notjerrygoh/Team-JRC-WRO-Future-Engineers-Engineering-Journal/schemes/Team JRC Robot Schematic Diagram (LT Spice Software)/Draft2.asc

BATTERY: voltage; 9V
X1: Rpi4B
X2: Ultrasonic
X3: Ultrasonic
X4: Ultrasonic
X5: Ultrasonic
X6: MotorDriver
X7: Motor
X8: Motor
X9: Servo
Named nets: 0, 5V_SHARED
