notjerrygoh/Team-JRC-WRO-Future-Engineers-Engineering-Journal/src/newdetect.py

# Run sudo pigpiod in terminal before running code

from gpiozero import Button, DistanceSensor
from gpiozero.pins.pigpio import PiGPIOFactory
from time import time
import pigpio
import numpy as np
import cv2
from picamera2 import Picamera2

pi = pigpio.pi()
button = Button(13, bounce_time=0.04, pull_up=True)

# Ultrasonic sensors
factory = PiGPIOFactory()
frontultrasonic = DistanceSensor(echo=5, trigger=6, max_distance=4, pin_factory=factory)
leftultrasonic = DistanceSensor(echo=17, trigger=4, max_distance=4, pin_factory=factory)
rightultrasonic = DistanceSensor(echo=27, trigger=22, max_distance=4, pin_factory=factory)
backultrasonic = DistanceSensor(echo=19, trigger=26, max_distance=4, pin_factory=factory)

turn_amt = 300
base_speed = 76
offset = 0

# Servo
servo_pin = 16
pwm = pigpio.pi()
pwm.set_mode(servo_pin, pigpio.OUTPUT)
pwm.set_PWM_frequency(servo_pin, 50)
pwm.set_servo_pulsewidth(servo_pin, 1500 + offset)  

# Camera
cam = Picamera2()
cam.configure(cam.create_preview_configuration({"size": (640, 360)}))
cam.start()


# Motors
M1A = 23
M1B = 24
pi.set_mode(M1A, pigpio.OUTPUT)
pi.set_mode(M1B, pigpio.OUTPUT)

# Motor speed
def motorSpeed(speed):
    if speed < 0:
        pi.set_PWM_dutycycle(M1A, abs(speed))
        pi.set_PWM_dutycycle(M1B, 0)
    elif speed > 0:
        pi.set_PWM_dutycycle(M1A, 0)
        pi.set_PWM_dutycycle(M1B, abs(speed))
    else:
        pi.set_PWM_dutycycle(M1A, 0)
        pi.set_PWM_dutycycle(M1B, 0)

# Orange line detection
last_orange_seen = -1
def detect_orange(frame, on_orange_line, lap_count):
    global last_orange_seen
    hsvFrame = cv2.cvtColor(frame, cv2.COLOR_BGR2HSV)
    orange_lower = np.array([5, 150, 150], np.uint8)
    orange_upper = np.array([20, 255, 255], np.uint8)
    orange_mask = cv2.inRange(hsvFrame, orange_lower, orange_upper)

    height, width = orange_mask.shape
    roi = orange_mask[height-60:height, :]
    orange_pixels = cv2.countNonZero(roi)

    ctime = time()
    crossed = False
    if orange_pixels > 1100:
        if not on_orange_line and (ctime - last_orange_seen) > 1.6:
            lap_count += 1
            crossed = True
            on_orange_line = True
            last_orange_seen = ctime
        elif (ctime - last_orange_seen) <= 1.6:
            print("Orange double count prevented")
    else:
        on_orange_line = False

    return lap_count, on_orange_line, crossed

# --- Blue line detection ---
last_blue_seen = -1
def detect_blue(frame, on_blue_line, lap_count):
    global last_blue_seen
    hsvFrame = cv2.cvtColor(frame, cv2.COLOR_BGR2HSV)
    blue_lower = np.array([100, 150, 20], np.uint8)
    blue_upper = np.array([130, 255, 255], np.uint8)
    blue_mask = cv2.inRange(hsvFrame, blue_lower, blue_upper)

    height, width = blue_mask.shape
    roi = blue_mask[height-60:height, :]
    blue_pixels = cv2.countNonZero(roi)

    ctime = time()

    crossed = False
    if blue_pixels > 1100:
        if not on_blue_line and (ctime - last_blue_seen) > 1.6:
            lap_count += 1
            crossed = True
            on_blue_line = True
            last_blue_seen = ctime
        elif (ctime - last_blue_seen) <= 1.6:
            print("Blue double count prevented")
    else:
        on_blue_line = False

    return lap_count, on_blue_line, crossed

# Red and green detection
def traffic_lights(frame):
    hsvFrame = cv2.cvtColor(frame, cv2.COLOR_BGR2HSV)

    # Red
    red_lower1 = np.array([0, 150, 50], np.uint8)
    red_upper1 = np.array([5, 255, 255], np.uint8)
    red_lower2 = np.array([172, 150, 100], np.uint8)
    red_upper2 = np.array([180, 255, 255], np.uint8)
    red_mask = cv2.inRange(hsvFrame, red_lower1, red_upper1) | cv2.inRange(hsvFrame, red_lower2, red_upper2)

    # Green
    green_lower = np.array([35, 50, 50], np.uint8)
    green_upper = np.array([85, 255, 255], np.uint8)
    green_mask = cv2.inRange(hsvFrame, green_lower, green_upper)

    kernel = np.ones((5, 5), "uint8")
    red_mask = cv2.dilate(red_mask, kernel)
    green_mask = cv2.dilate(green_mask, kernel)


    def detect_and_label(mask, color_bgr, label):
        contours, _ = cv2.findContours(mask, cv2.RETR_TREE, cv2.CHAIN_APPROX_SIMPLE)
        if not contours:
            return 0, None
        largest = max(contours, key=cv2.contourArea)
        area = cv2.contourArea(largest)
        if 20000 < area < 60000:  # stable area range
            x, y, w, h = cv2.boundingRect(largest)
            cv2.rectangle(frame, (x, y), (x + w, y + h), color_bgr, 2)
            return area, label
        return 0, None

    red_area, red_label = detect_and_label(red_mask, (0, 0, 255), "Red")
    green_area, green_label = detect_and_label(green_mask, (0, 255, 0), "Green")

    return red_area, green_area, red_label, green_label


lap_count = 0
on_orange_line = False
orange_sequence = None  
servo_sequence = None  
stable_counter = 0  
is_orange = 0

# wait for start
print("Waiting...")
button.wait_for_press()
print("Robot Started!")

try:
    while True:

        try:
            frame = cv2.cvtColor(cam.capture_array()[::-1, :, :3], cv2.COLOR_RGB2BGR)
            camera_ok = True
        except Exception:
            camera_ok = False

        distance_cm = frontultrasonic.distance * 100
        current_time = time()


        if camera_ok and lap_count < 12: 
            crossed = False
            if is_orange == 0:
                lap_count, on_orange_line, crossed = detect_orange(frame, on_orange_line, lap_count)
                if lap_count == 1:
                    is_orange = 1
                    turn_amt = 200
                else:
                    lap_count, on_orange_line, crossed = detect_blue(frame, on_orange_line, lap_count)
                    if lap_count == 1:
                        is_orange = -1
                        turn_amt = -200
            elif is_orange == 1:
                lap_count, on_orange_line, crossed = detect_blue(frame, on_orange_line, lap_count)
            elif is_orange == -1:
                lap_count, on_orange_line, crossed = detect_orange(frame, on_orange_line, lap_count)

            motorSpeed(base_speed)

            if crossed and orange_sequence is None:
                orange_sequence = ([(1500 + offset, 0), (1500 + offset + turn_amt, 1.7), (1500 + offset,0)], 0, current_time)
                print(f"Lap {lap_count} completed")

            if orange_sequence is not None:
                steps, step_index, start_time = orange_sequence
                pos, duration = steps[step_index]
                pwm.set_servo_pulsewidth(servo_pin, pos)

                if current_time - start_time >= duration:
                    step_index += 1
                    if step_index >= len(steps):
                        orange_sequence = None
                    else:
                        orange_sequence = (steps, step_index, current_time)

            red_area, green_area, red_label, green_label = traffic_lights(frame)

            if red_area > green_area or green_area > red_area:
                stable_counter += 1
            else:
                stable_counter = 0

            if servo_sequence is None and stable_counter >= 3: 
                if red_area > green_area:
                    servo_sequence = ([(1500 + offset + turn_amt, 1), (1500 + offset, 1), (1500 + offset - turn_amt, 1), (1500 + offset, 0)], 0, current_time + 0.1)
                    color_detected = red_label
                elif green_area > red_area:
                    servo_sequence = ([(1500 + offset - turn_amt, 1), (1500 + offset, 1), (1500 + offset + turn_amt, 1), (1500 + offset, 0)], 0, current_time + 0.1)
                    color_detected = green_label
                else:
                    pwm.set_servo_pulsewidth(servo_pin, 1500 + offset)
                    color_detected = "None"
            elif servo_sequence is not None:
                orange_sequence = None
                steps, step_index, start_time = servo_sequence
                pos, duration = steps[step_index]
                pwm.set_servo_pulsewidth(servo_pin, pos)

                if current_time - start_time >= duration:
                    step_index += 1
                    if step_index >= len(steps):
                        servo_sequence = None
                    else:
                        servo_sequence = (steps, step_index, current_time)
                color_detected = red_label if red_area > green_area else green_label
            else:
                color_detected = "None"
            print("Detected:", color_detected, stable_counter, red_area, green_area)
            # cv2.imshow("Color Detection", frame)

"""
            left_dist = leftultrasonic.distance * 100
            right_dist = rightultrasonic.distance * 100
            # print("Servo distances: ", int(left_dist), int(right_dist))
            if left_dist < 32:
                pwm.set_servo_pulsewidth(servo_pin, (1500 + offset + 200))
                motorSpeed(base_speed)
            elif right_dist < 32:
                pwm.set_servo_pulsewidth(servo_pin, (1500 + offset - 200))
                motorSpeed(base_speed)
            elif servo_sequence is None and orange_sequence is None:
                pwm.set_servo_pulsewidth(servo_pin, 1500 + offset)
"""

        if cv2.waitKey(10) & 0xFF == ord('q'):
            motorSpeed(0)
            break

finally:
    motorSpeed(0)
    pwm.set_servo_pulsewidth(servo_pin, 0)
    cv2.destroyAllWindows()
